NazaFF/Autonomous-Mobile-Robot-Control-System/Software/Test_Code/find_IR/find_IR.ino

//Descobrir que códigos imite o comando

#include <IRremote.h>

const int RECV_PIN = 7;
IRrecv irrecv(RECV_PIN);
decode_results results;

void setup(){
  Serial.begin(9600);
  irrecv.enableIRIn();
  irrecv.blink13(true);
}

void loop(){
  if (irrecv.decode(&results)){
        Serial.println(results.value, HEX);
        irrecv.resume();
  }
}
