NazaFF/Autonomous-Mobile-Robot-Control-System/Software/Test_Code/Ultrasound_test/US_teste.ino

long duration;         //duration of ultrasonic pulse
int distanceCm;        //distance in cm
void setup() {
  Serial.begin (9600);
  pinMode(A4, OUTPUT);    //Analog pin A1 connected to TRIG
  pinMode(A3, INPUT);     //Analog pin A0 connected to ECHO
}
void loop()
{
  digitalWrite(A4, LOW);
  delayMicroseconds(2);
  digitalWrite(A4, HIGH);    //give a pulse of 10us on TRIG
  delayMicroseconds(10);
  digitalWrite(A4, LOW);
  duration = pulseIn(A3, HIGH);     //check time elasped in receiving back the pulse on ECHO
  distanceCm = duration * 0.034 / 2; //convert to distance in cm
  if (distanceCm <= 20)          //if distance less than 20cm display on monitor
  {
    Serial.println(distanceCm);
    delay(1000);
  }
  else
  {}
}
